jsr38/crocolulo/simulations/fig/i_l1_0.5_3.6.png

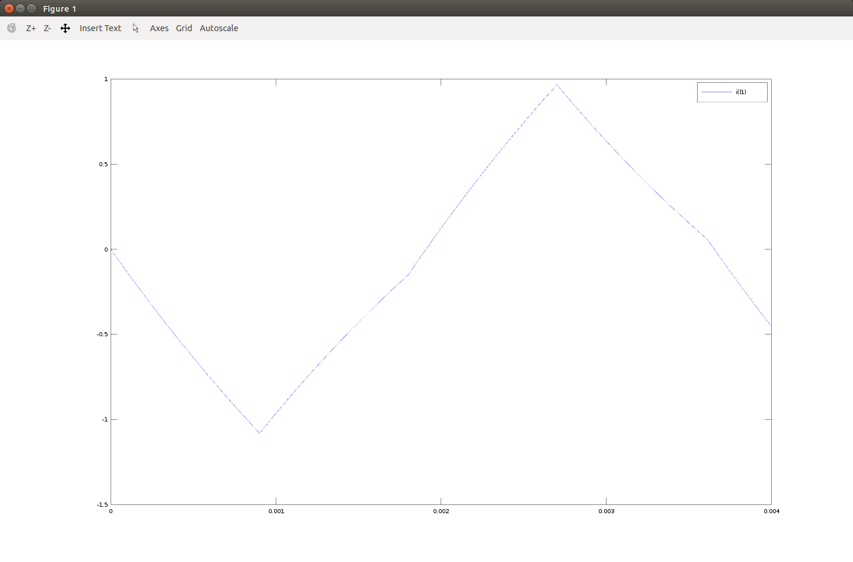
simulations/fig/i_l1_0.5_3.6.png
