jsr38/crocolulo/simulations/fig/v_i_l1.png

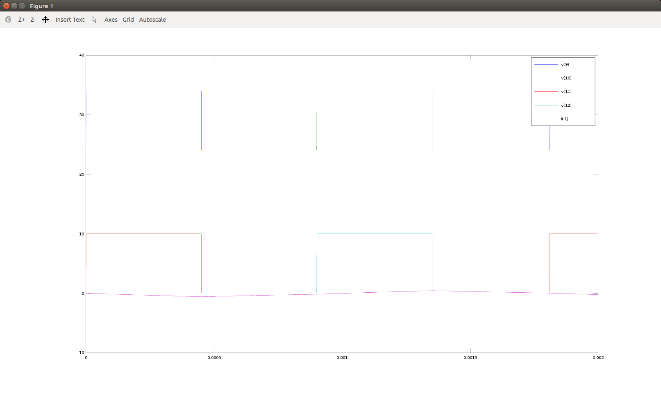
simulations/fig/v_i_l1.png
